yanataka60/PASOPIA7_SD/JPEG/PASOPIA7_SD(3).jpg

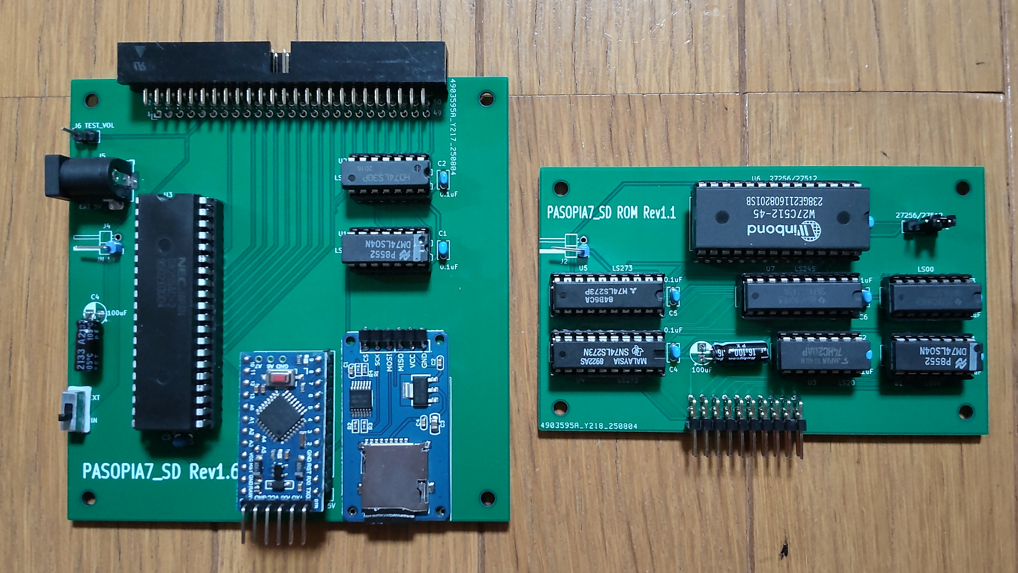
JPEG/PASOPIA7_SD(3).jpg
