yanataka60/PASOPIA7_SD/JPEG/TITLE_PASOPIA.jpg

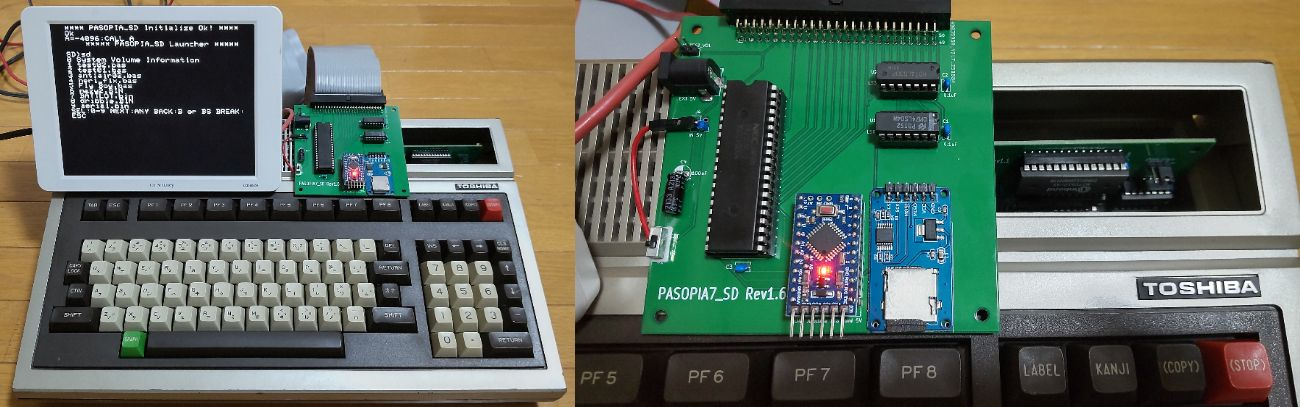
JPEG/TITLE_PASOPIA.jpg
